akkdong/Cube/doc/ESP32-S3-HMI-V3/ESP32-S3-HMI-V3-connector.png

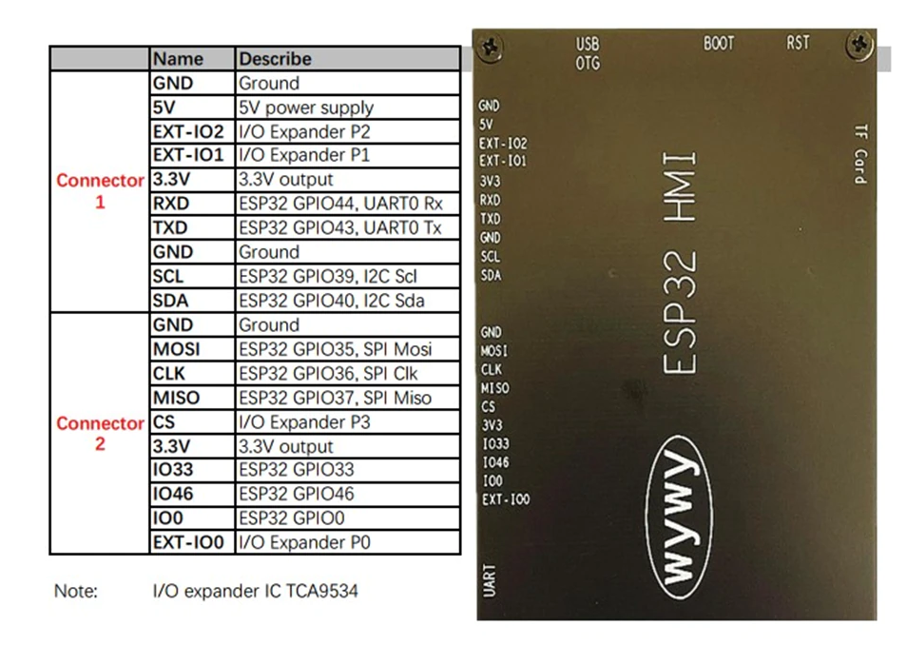
doc/ESP32-S3-HMI-V3/ESP32-S3-HMI-V3-connector.png
