akkdong/Cube/doc/ESP32_WT32-SC01/bmp280-module.png

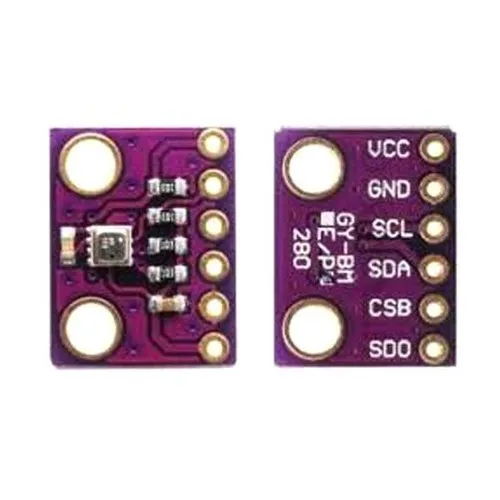
doc/ESP32_WT32-SC01/bmp280-module.png
