akkdong/Cube/doc/ESP32_WT32-SC01/ESP32_WT32-SC01_back.webp

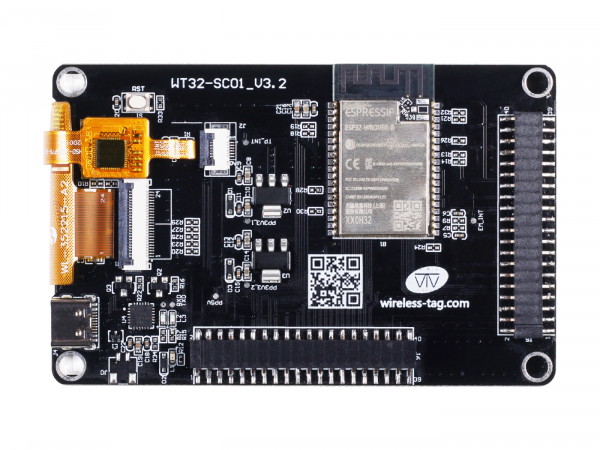
doc/ESP32_WT32-SC01/ESP32_WT32-SC01_back.webp
