akkdong/Cube/doc/ESP32_WT32-SC01/ESP32_WT32-SC01_front.webp

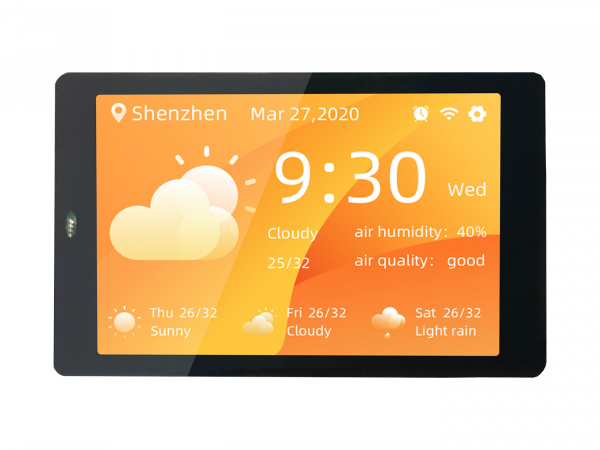
doc/ESP32_WT32-SC01/ESP32_WT32-SC01_front.webp
