akkdong/Cube/doc/ESP32_WT32-SC01/PA6C1V1721-2.jpg

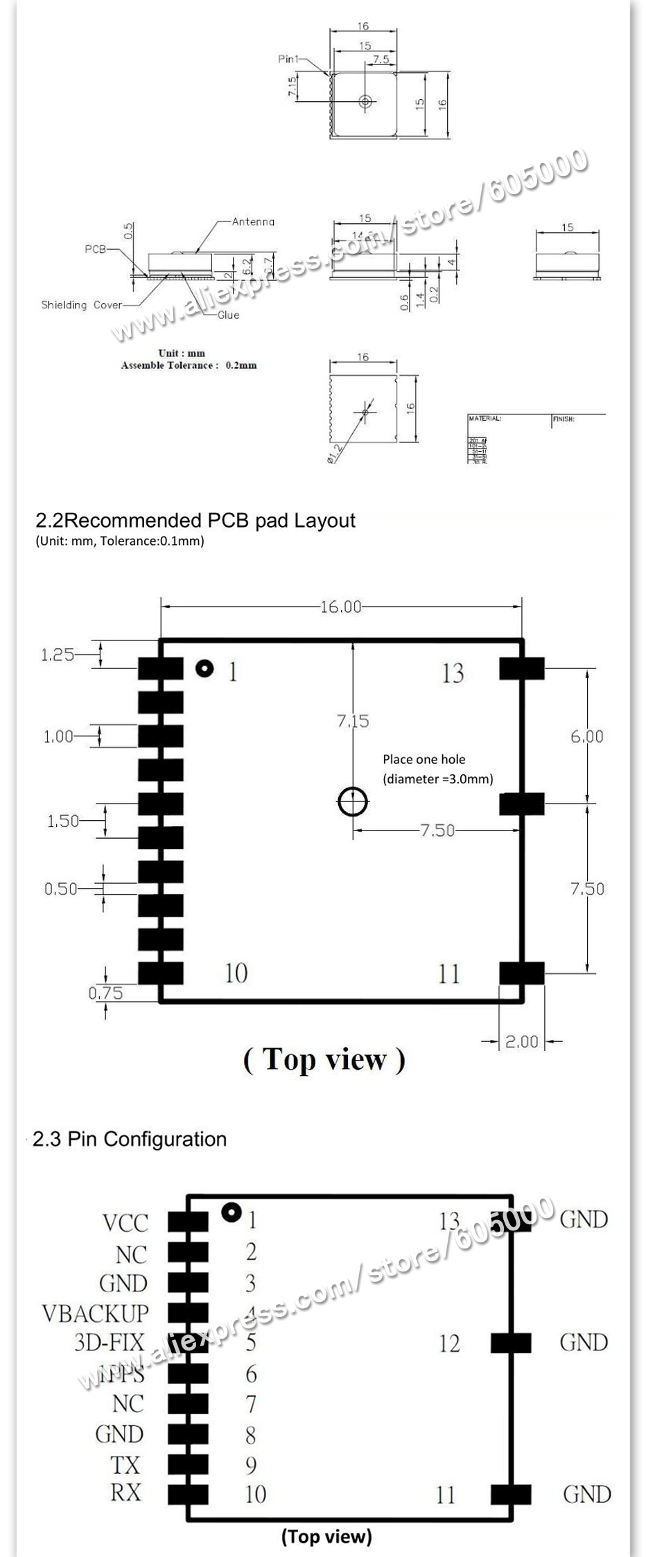
doc/ESP32_WT32-SC01/PA6C1V1721-2.jpg
