akkdong/Cube/doc/m2-working.jpg

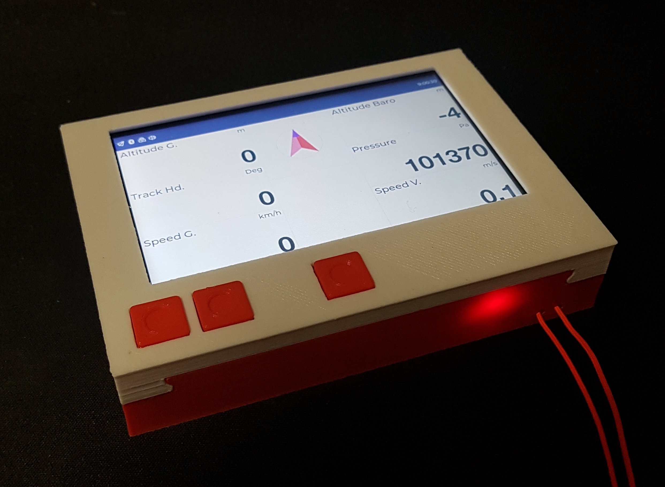
doc/m2-working.jpg
