akkdong/Cube/doc/cube-m1-assembly.jpg

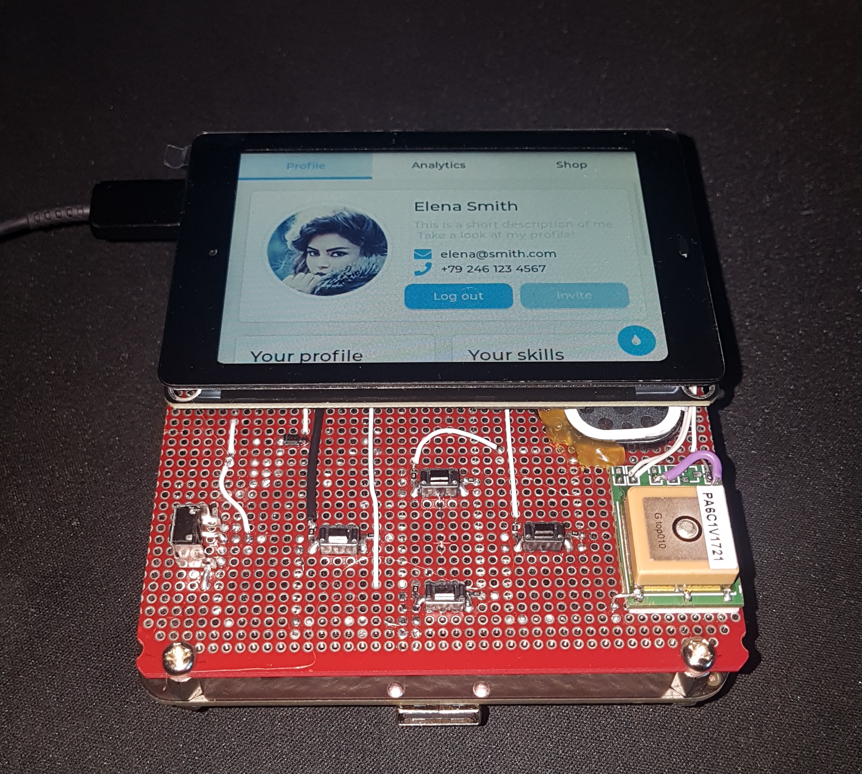
doc/cube-m1-assembly.jpg
