akkdong/Cube/M3/disp/src/main.cpp

// main.cpp
//

#include <Arduino.h>
#include <M5EPD.h>
#include <WiFi.h>
#include <WebServer.h>
#include <Update.h>
#include <ArduinoEigen.h>
#include <ArduinoJson.h>
#include <GeographicLib/Geodesic.hpp>

#include "board.h"
#include "utils.h"
#include "timezone.h"
#include "logger.h"
#include "agl.h"
#include "CriticalSection.h"
#include "NmeaParser.h"
#include "Keypad.h"
#include "Window.h"
#include "Widgets.h"
#include "VarioSentence.h"
#include "VarioLogger.h"
#include "Application.h"
#include "BLEVario.h"
#include "CaptivePortal.h"
#include "Route.h"


//
//
//
//
//




//
//
//
//
//

Application App;


Application* Application::getApp()
{
    return &App;
}


void setup()
{
    //
    // BSP initialize
    //
    Application::initBoard();


    //
    //
    //
    App.begin();
}

void loop()
{
    //
    //
    //
    App.update();
}
