akkdong/Cube/M2/src/assets/startup_a.c

#if 0
#ifdef __has_include
    #if __has_include("lvgl.h")
        #ifndef LV_LVGL_H_INCLUDE_SIMPLE
            #define LV_LVGL_H_INCLUDE_SIMPLE
        #endif
    #endif
#endif

#if defined(LV_LVGL_H_INCLUDE_SIMPLE)
    #include "lvgl.h"
#else
    #include "lvgl/lvgl.h"
#endif
#else
#include <lvgl.h>
#endif

#ifndef LV_ATTRIBUTE_MEM_ALIGN
#define LV_ATTRIBUTE_MEM_ALIGN
#endif

#ifndef LV_ATTRIBUTE_IMG_STARTUP_A
#define LV_ATTRIBUTE_IMG_STARTUP_A
#endif

const LV_ATTRIBUTE_MEM_ALIGN LV_ATTRIBUTE_LARGE_CONST LV_ATTRIBUTE_IMG_STARTUP_A uint8_t startup_a_map[] = {
  0xfe, 0xfe, 0xfe, 0xff, 	/*Color of index 0*/
  0x30, 0x30, 0x30, 0xff, 	/*Color of index 1*/
  0x02, 0x02, 0x02, 0xff, 	/*Color of index 2*/
  0xfd, 0xfe, 0xe7, 0xff, 	/*Color of index 3*/
  0xf1, 0xe8, 0xb7, 0xff, 	/*Color of index 4*/
  0xf3, 0xd1, 0x7c, 0xff, 	/*Color of index 5*/
  0xdf, 0xb7, 0x53, 0xff, 	/*Color of index 6*/
  0xa4, 0xa4, 0xa3, 0xff, 	/*Color of index 7*/
  0xce, 0xa3, 0x36, 0xff, 	/*Color of index 8*/
  0xee, 0xad, 0x02, 0xff, 	/*Color of index 9*/
  0xd0, 0x9b, 0x12, 0xff, 	/*Color of index 10*/
  0x65, 0x64, 0x64, 0xff, 	/*Color of index 11*/
  0xf4, 0xf1, 0xf5, 0xff, 	/*Color of index 12*/
  0xc1, 0xa2, 0xf5, 0xff, 	/*Color of index 13*/
  0x80, 0x5a, 0xcd, 0xff, 	/*Color of index 14*/
  0x58, 0x1a, 0xd2, 0xff, 	/*Color of index 15*/

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
};

const lv_img_dsc_t startup_a = {
  .header.cf = LV_IMG_CF_INDEXED_4BIT,
  .header.always_zero = 0,
  .header.reserved = 0,
  .header.w = 404,
  .header.h = 316,
  .data_size = 63896,
  .data = startup_a_map,
};
