akkdong/Cube/M2/src/assets/goodbye.c

#if 0
#ifdef __has_include
    #if __has_include("lvgl.h")
        #ifndef LV_LVGL_H_INCLUDE_SIMPLE
            #define LV_LVGL_H_INCLUDE_SIMPLE
        #endif
    #endif
#endif
#if defined(LV_LVGL_H_INCLUDE_SIMPLE)
    #include "lvgl.h"
#else
    #include "lvgl/lvgl.h"
#endif
#else
#include <lvgl.h>
#endif


#ifndef LV_ATTRIBUTE_MEM_ALIGN
#define LV_ATTRIBUTE_MEM_ALIGN
#endif

#ifndef LV_ATTRIBUTE_IMG_GOODBYE
#define LV_ATTRIBUTE_IMG_GOODBYE
#endif

const LV_ATTRIBUTE_MEM_ALIGN LV_ATTRIBUTE_LARGE_CONST LV_ATTRIBUTE_IMG_GOODBYE uint8_t goodbye_map[] = {
  0x00, 0x00, 0x00, 0x00, 	/*Color of index 0*/
  0xff, 0xff, 0xff, 0x06, 	/*Color of index 1*/
  0x00, 0x00, 0xff, 0x01, 	/*Color of index 2*/
  0xaa, 0xaa, 0xff, 0x03, 	/*Color of index 3*/
  0xf5, 0xf5, 0xff, 0x1a, 	/*Color of index 4*/
  0xf5, 0xf5, 0xfc, 0x2b, 	/*Color of index 5*/
  0x00, 0x00, 0x80, 0x02, 	/*Color of index 6*/
  0x55, 0x55, 0xaa, 0x03, 	/*Color of index 7*/
  0x9c, 0x9c, 0xd5, 0x06, 	/*Color of index 8*/
  0xc3, 0xc3, 0xe9, 0x0b, 	/*Color of index 9*/
  0x80, 0x80, 0xd4, 0x06, 	/*Color of index 10*/
  0x00, 0x00, 0xaa, 0x03, 	/*Color of index 11*/
  0x78, 0x78, 0xc2, 0x06, 	/*Color of index 12*/
  0x00, 0x00, 0xbe, 0x04, 	/*Color of index 13*/
  0xef, 0xef, 0xfb, 0x40, 	/*Color of index 14*/
  0xb0, 0xb0, 0xec, 0x0e, 	/*Color of index 15*/
  0x00, 0x00, 0xcb, 0x05, 	/*Color of index 16*/
  0x00, 0x00, 0xd7, 0x06, 	/*Color of index 17*/
  0x23, 0x23, 0xdb, 0x07, 	/*Color of index 18*/
  0xed, 0xed, 0xf8, 0x51, 	/*Color of index 19*/
  0x20, 0x40, 0xdf, 0x08, 	/*Color of index 20*/
  0x8c, 0x8e, 0xea, 0x0e, 	/*Color of index 21*/
  0xbf, 0xbf, 0xf1, 0x1a, 	/*Color of index 22*/
  0xa4, 0xa0, 0xe8, 0x12, 	/*Color of index 23*/
  0x24, 0x00, 0xd1, 0x07, 	/*Color of index 24*/
  0x1c, 0x1c, 0xc6, 0x09, 	/*Color of index 25*/
  0x8a, 0x83, 0xe3, 0x12, 	/*Color of index 26*/
  0x1a, 0x1a, 0xcc, 0x0a, 	/*Color of index 27*/
  0xf6, 0xf6, 0xfc, 0xff, 	/*Color of index 28*/
  0xe8, 0xe8, 0xf8, 0x6a, 	/*Color of index 29*/
  0x15, 0x15, 0xd2, 0x0b, 	/*Color of index 30*/
  0xb1, 0xb3, 0xee, 0x23, 	/*Color of index 31*/
  0x28, 0x14, 0xd6, 0x0c, 	/*Color of index 32*/
  0x14, 0x14, 0xc3, 0x0c, 	/*Color of index 33*/
  0xa5, 0xa5, 0xe9, 0x22, 	/*Color of index 34*/
  0x16, 0x28, 0xcc, 0x0f, 	/*Color of index 35*/
  0x21, 0x21, 0xce, 0x0f, 	/*Color of index 36*/
  0x11, 0x11, 0xc9, 0x0e, 	/*Color of index 37*/
  0x92, 0x92, 0xe2, 0x1f, 	/*Color of index 38*/
  0xe3, 0xe3, 0xf7, 0x80, 	/*Color of index 39*/
  0x00, 0x11, 0xbb, 0x0f, 	/*Color of index 40*/
  0x10, 0x10, 0xcf, 0x10, 	/*Color of index 41*/
  0x1d, 0x1d, 0xd3, 0x11, 	/*Color of index 42*/
  0x10, 0x0e, 0xc3, 0x11, 	/*Color of index 43*/
  0x1a, 0x0c, 0xca, 0x13, 	/*Color of index 44*/
  0x19, 0x19, 0xcb, 0x14, 	/*Color of index 45*/
  0x0c, 0x0c, 0xc9, 0x13, 	/*Color of index 46*/
  0x0e, 0x0c, 0xd0, 0x14, 	/*Color of index 47*/
  0x92, 0x91, 0xe7, 0x2d, 	/*Color of index 48*/
  0x84, 0x83, 0xe2, 0x28, 	/*Color of index 49*/
  0x00, 0x00, 0xce, 0x14, 	/*Color of index 50*/
  0x16, 0x16, 0xd1, 0x16, 	/*Color of index 51*/
  0xe9, 0xea, 0xf9, 0xff, 	/*Color of index 52*/
  0x22, 0x22, 0xd0, 0x19, 	/*Color of index 53*/
  0x16, 0x0b, 0xc7, 0x17, 	/*Color of index 54*/
  0xa7, 0xa7, 0xec, 0x41, 	/*Color of index 55*/
  0xdc, 0xdd, 0xf6, 0xa8, 	/*Color of index 56*/
  0x0a, 0x0a, 0xca, 0x18, 	/*Color of index 57*/
  0x14, 0x14, 0xca, 0x19, 	/*Color of index 58*/
  0x1b, 0x1b, 0xce, 0x1b, 	/*Color of index 59*/
  0xb5, 0xb4, 0xf1, 0x55, 	/*Color of index 60*/
  0x12, 0x12, 0xd0, 0x1c, 	/*Color of index 61*/
  0x11, 0x11, 0xc9, 0x1d, 	/*Color of index 62*/
  0x16, 0x18, 0xce, 0x1f, 	/*Color of index 63*/
  0xe2, 0xe2, 0xf7, 0xfe, 	/*Color of index 64*/
  0x23, 0x23, 0xd1, 0x24, 	/*Color of index 65*/
  0x15, 0x15, 0xce, 0x23, 	/*Color of index 66*/
  0x0f, 0x0e, 0xcc, 0x22, 	/*Color of index 67*/
  0xa0, 0xa0, 0xed, 0x57, 	/*Color of index 68*/
  0x1b, 0x1b, 0xcf, 0x25, 	/*Color of index 69*/
  0xd5, 0xd6, 0xf4, 0xcc, 	/*Color of index 70*/
  0x13, 0x13, 0xc9, 0x25, 	/*Color of index 71*/
  0x0f, 0x0c, 0xcb, 0x25, 	/*Color of index 72*/
  0x23, 0x23, 0xd2, 0x2a, 	/*Color of index 73*/
  0xda, 0xdb, 0xf5, 0xfe, 	/*Color of index 74*/
  0xaf, 0xaf, 0xee, 0x77, 	/*Color of index 75*/
  0x19, 0x1a, 0xce, 0x2a, 	/*Color of index 76*/
  0x12, 0x12, 0xce, 0x2a, 	/*Color of index 77*/
  0x89, 0x89, 0xe7, 0x57, 	/*Color of index 78*/
  0x11, 0x11, 0xcb, 0x2b, 	/*Color of index 79*/
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
};

const lv_img_dsc_t goodbye = {
  .header.cf = LV_IMG_CF_INDEXED_8BIT,
  .header.always_zero = 0,
  .header.reserved = 0,
  .header.w = 320,
  .header.h = 215,
  .data_size = 69824,
  .data = goodbye_map,
};
