akkdong/Cube/M2/src/assets/startup.c

#if 0
#if defined(LV_LVGL_H_INCLUDE_SIMPLE)
#include "lvgl.h"
#else
#include "lvgl/lvgl.h"
#endif
#else
#include <lvgl.h>
#endif


#ifndef LV_ATTRIBUTE_MEM_ALIGN
#define LV_ATTRIBUTE_MEM_ALIGN
#endif

#ifndef LV_ATTRIBUTE_IMG_STARTUP
#define LV_ATTRIBUTE_IMG_STARTUP
#endif

const LV_ATTRIBUTE_MEM_ALIGN LV_ATTRIBUTE_LARGE_CONST LV_ATTRIBUTE_IMG_STARTUP uint8_t startup_map[] = {
  0xfe, 0xfe, 0xfe, 0xff, 	/*Color of index 0*/
  0xf3, 0xf3, 0xf3, 0xff, 	/*Color of index 1*/
  0xe8, 0xe8, 0xe8, 0xff, 	/*Color of index 2*/
  0xda, 0xda, 0xda, 0xff, 	/*Color of index 3*/
  0xcd, 0xcd, 0xcd, 0xff, 	/*Color of index 4*/
  0xba, 0xba, 0xba, 0xff, 	/*Color of index 5*/
  0xa1, 0xa1, 0xa1, 0xff, 	/*Color of index 6*/
  0x8a, 0x8a, 0x8a, 0xff, 	/*Color of index 7*/
  0x72, 0x72, 0x72, 0xff, 	/*Color of index 8*/
  0x59, 0x59, 0x59, 0xff, 	/*Color of index 9*/
  0x44, 0x44, 0x44, 0xff, 	/*Color of index 10*/
  0x2f, 0x2f, 0x2f, 0xff, 	/*Color of index 11*/
  0x1f, 0x1f, 0x1f, 0xff, 	/*Color of index 12*/
  0x13, 0x13, 0x13, 0xff, 	/*Color of index 13*/
  0x09, 0x09, 0x09, 0xff, 	/*Color of index 14*/
  0x00, 0x00, 0x00, 0xff, 	/*Color of index 15*/

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
  0x00, 0x00, 0x00, 0x00, 0x00, 0x00, 0x00, 0x00, 0x00, 0x00, 0x00, 0x00, 0x00, 0x00, 0x00, 0x00, 0x00, 0x00, 0x00, 0x00, 0x00, 0x00, 0x00, 0x00, 0x00, 0x00, 0x00, 0x00, 0x00, 0x00, 0x00, 0x00, 0x00, 0x00, 0x00, 0x00, 0x07, 0xef, 0xff, 0xff, 0xff, 0xff, 0xff, 0xff, 0xff, 0xf9, 0x02, 0xcf, 0xff, 0xff, 0xff, 0xff, 0xff, 0x7e, 0xff, 0xff, 0xff, 0xff, 0xff, 0xff, 0x93, 0x00, 0x00, 0x00, 0x00, 0x00, 0x00, 0x00, 0x00, 0x00, 0x00, 0x00, 0x00, 0x00, 0x00, 0x00, 0x00, 0xcf, 0xd1, 0x00, 0x00, 0x00, 0x00, 0x00, 0x00, 0x00, 0x00, 0x00, 0x00, 0x00, 0x00, 0x00, 0x00, 0x00, 0x00, 0x00, 0x00, 0x00, 0x00, 0x00, 0x00, 0x00, 0x00, 0x00, 0x00, 0x00, 0x00, 0x00, 0x00, 0x00, 0x00, 0x00, 0x00, 0x00, 0x00, 0x00, 0x00, 0x00, 0x00, 0x00, 0x00, 0x00, 0x00, 0x00, 0x00, 0x00, 0x00, 0x00, 0x00, 0x00, 0x00, 0x00, 0x00, 0x00, 0x00, 0x00, 0x00, 0x00, 0x00, 0x00, 0x00, 0x00, 0x00, 0x00, 0x00, 0x00, 0x00, 0x00, 0x00, 0x00, 0x00, 0x00, 0x00, 0x00, 0x00, 0x00, 0x00, 0x00, 0x00, 0x00,
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
